CarbonComputers/Cybert/Hardware/Display/YX40006ACT Display Spec/LCD/时序参考timing.png

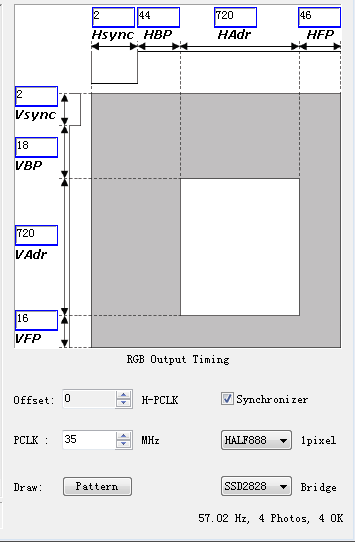
Hardware/Display/YX40006ACT Display Spec/LCD/时序参考timing.png
