CarbonComputers/Cybert/Hardware/PCB/Cybert 3.0 Back.jpg

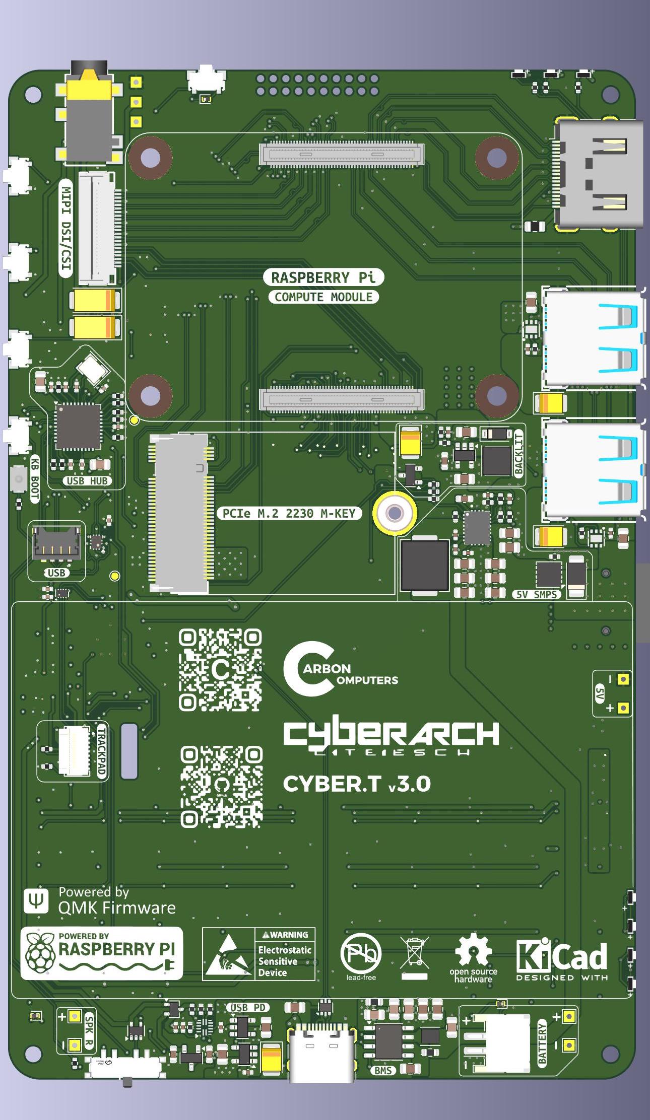
Hardware/PCB/Cybert 3.0 Back.jpg
