CarbonComputers/Cybert/Hardware/PCB/Cybert 3.0 Front.jpg

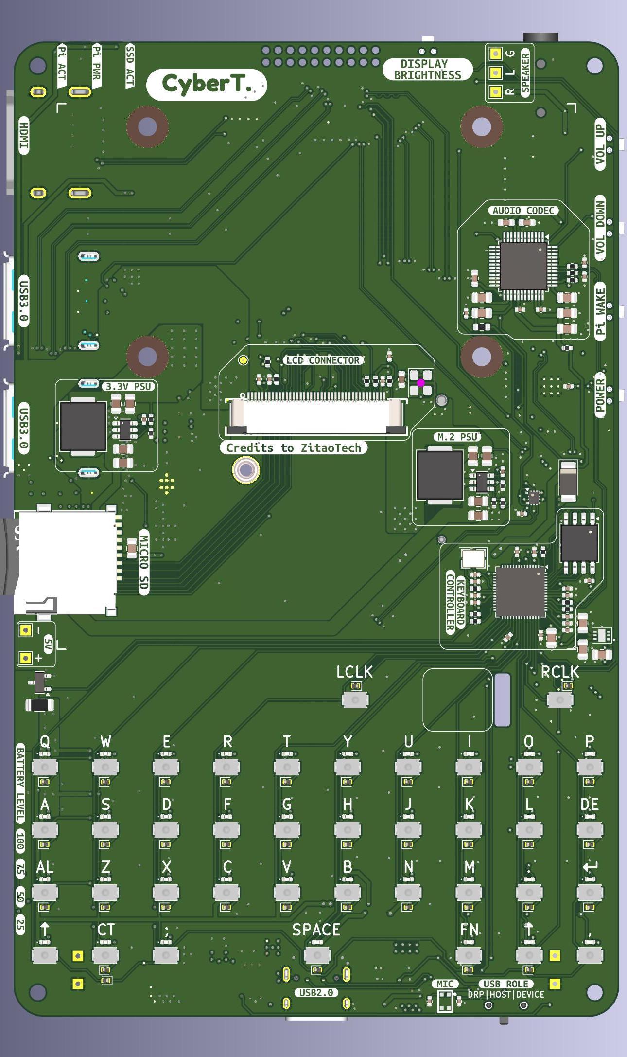
Hardware/PCB/Cybert 3.0 Front.jpg
