CarbonComputers/Cybert/Hardware/Renders/1.jpg

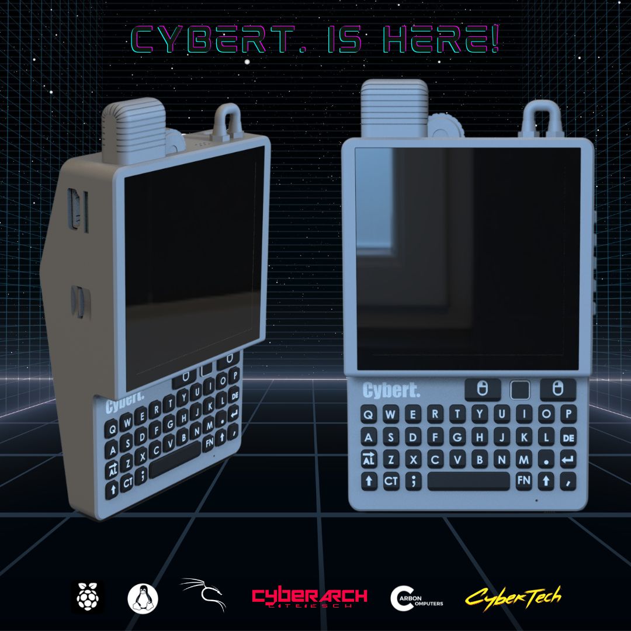
Hardware/Renders/1.jpg
