CarbonComputers/Cybert/Hardware/Renders/2.jpg

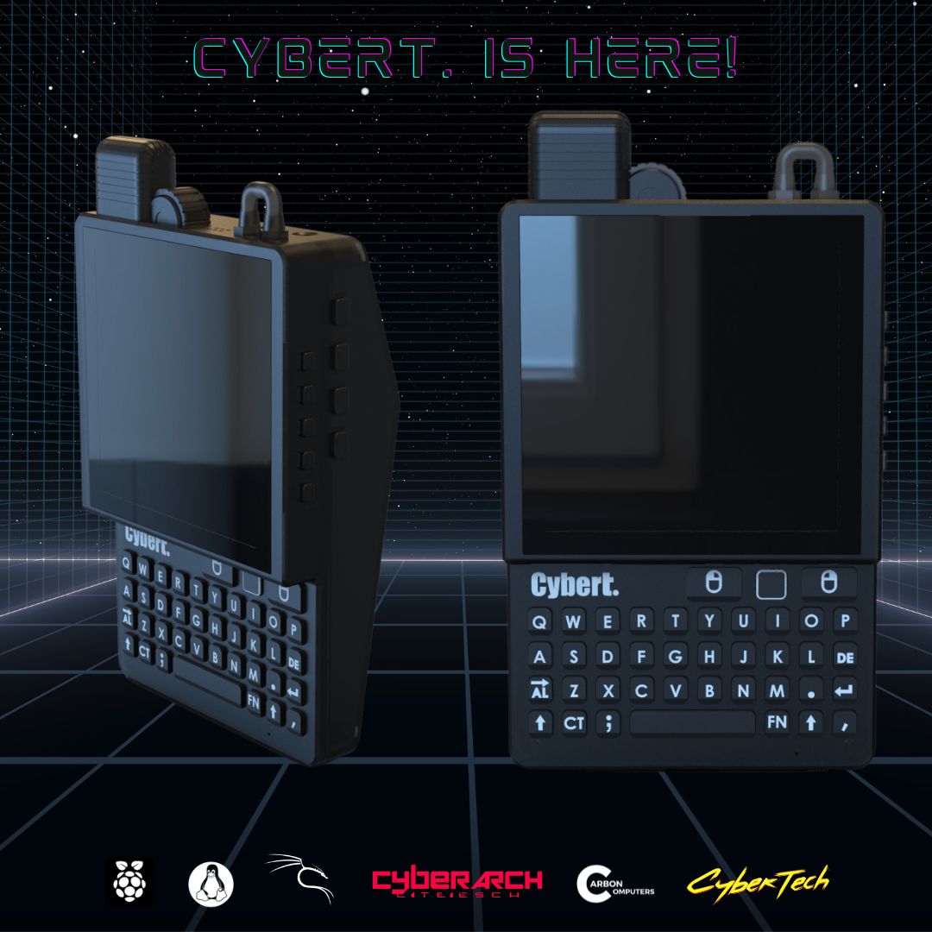
Hardware/Renders/2.jpg
