CarbonComputers/Cybert/Hardware/Renders/5.jpg

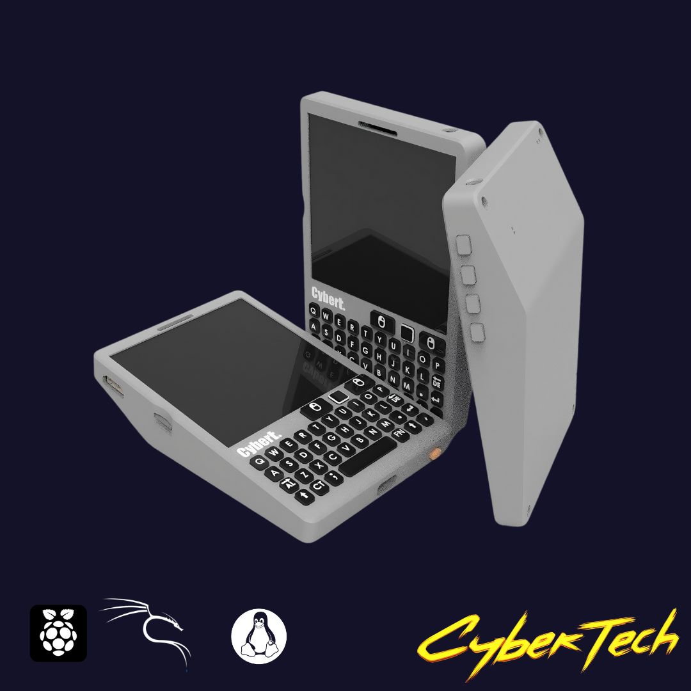
Hardware/Renders/5.jpg
