CarbonComputers/Cybert/Hardware/Renders/6.jpg

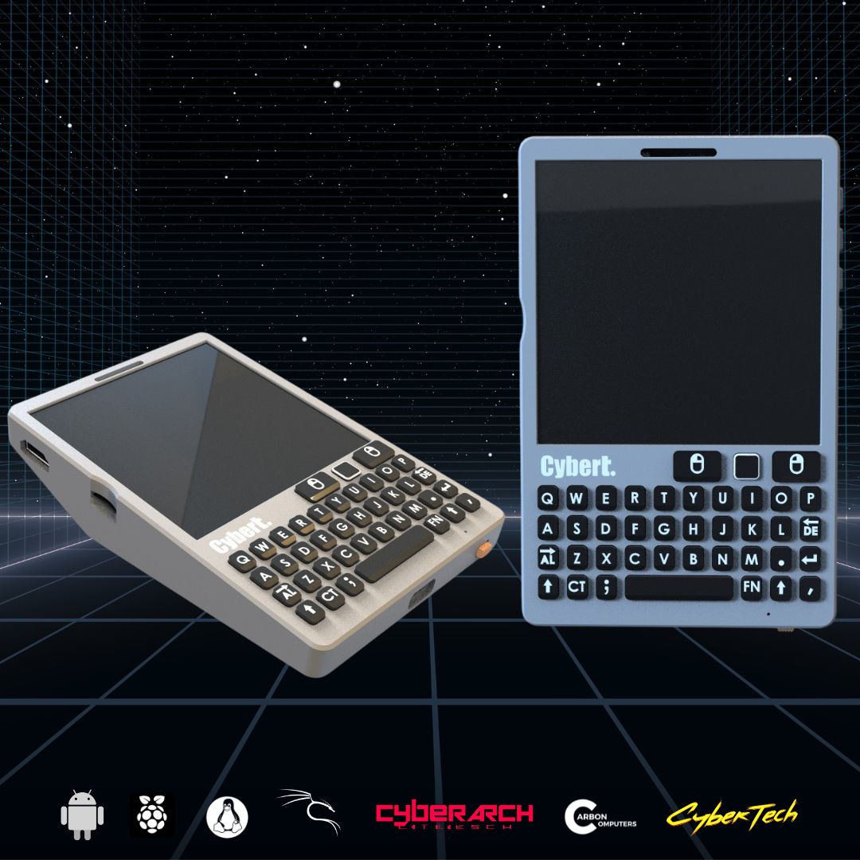
Hardware/Renders/6.jpg
