CarbonComputers/Cybert/Hardware/Renders/7.jpg

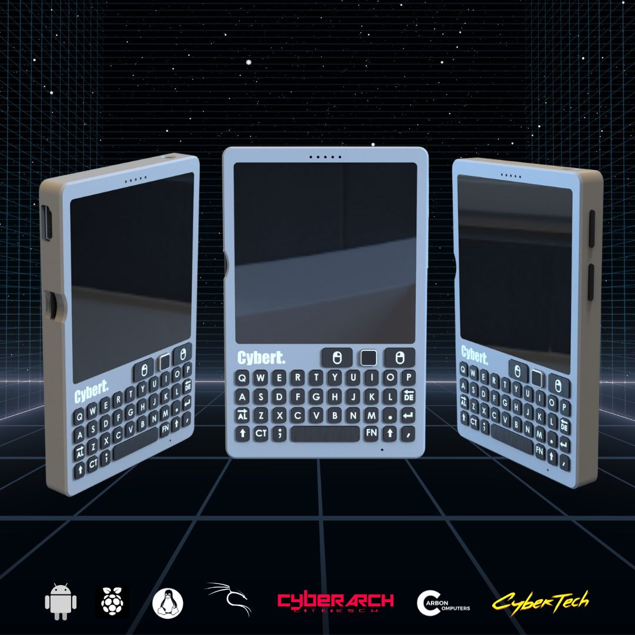
Hardware/Renders/7.jpg
