CarbonComputers/Cybert/Hardware/Renders/18.jpg

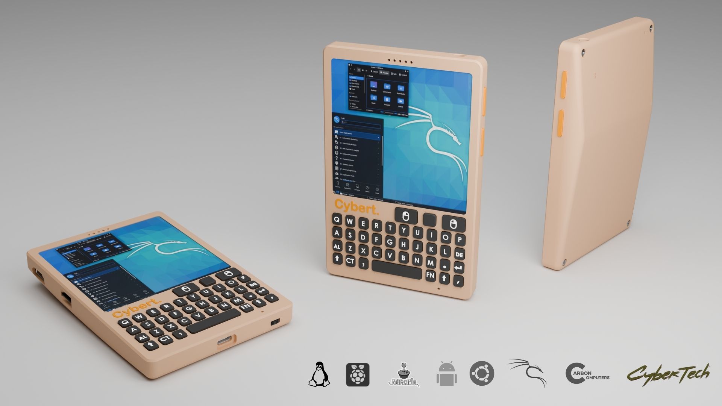
Hardware/Renders/18.jpg
