CarbonComputers/Cybert/Hardware/Renders/19.jpg

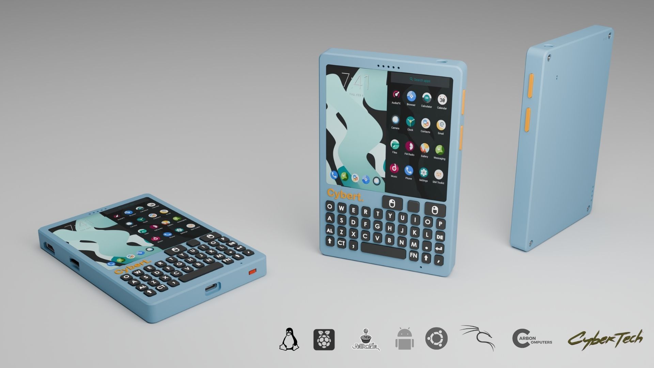
Hardware/Renders/19.jpg
