CarbonComputers/Cybert/Hardware/Renders/20.jpg

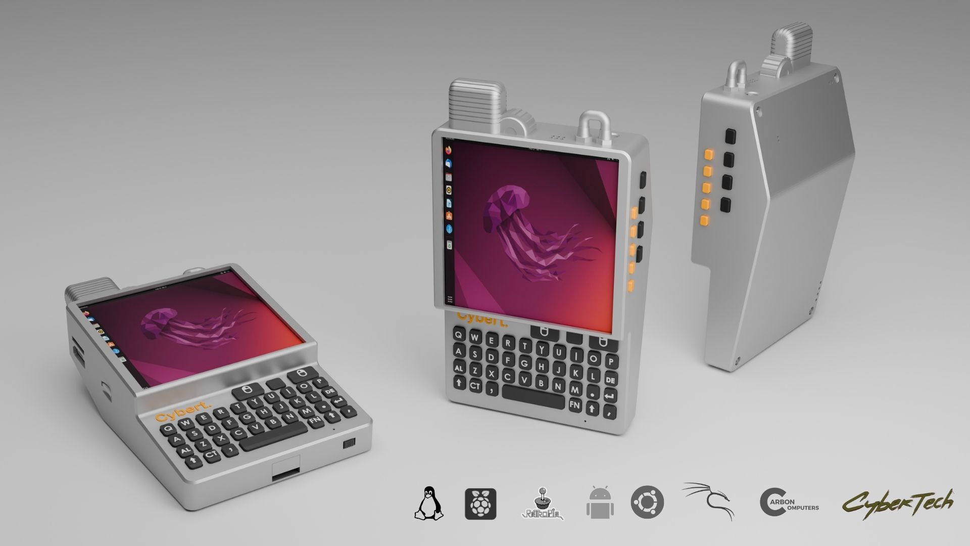
Hardware/Renders/20.jpg
