CarbonComputers/Cybert/Hardware/Renders/21.jpg

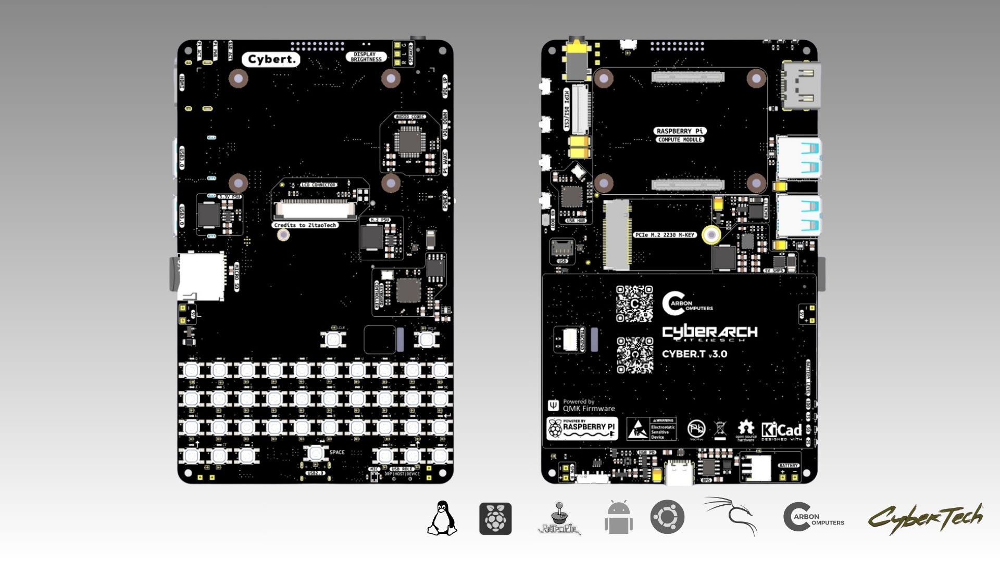
Hardware/Renders/21.jpg
