CarbonComputers/Cybert/Hardware/Renders/Cybert 3.2.1.jpeg

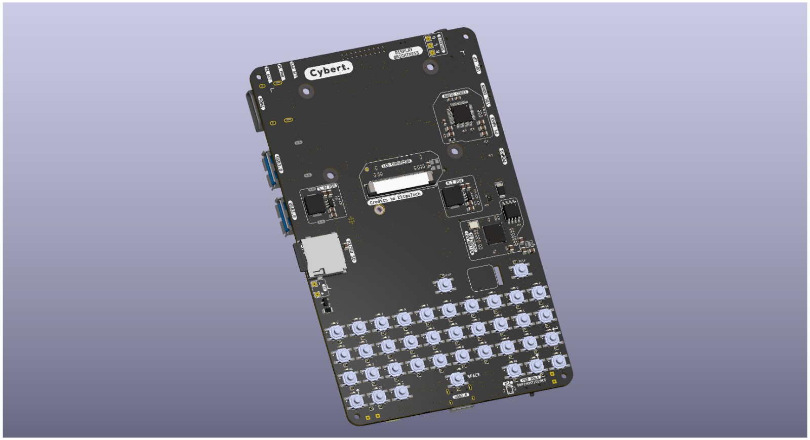
Hardware/Renders/Cybert 3.2.1.jpeg
