CarbonComputers/Cybert/Hardware/Renders/Cybert 3.2.2.jpeg

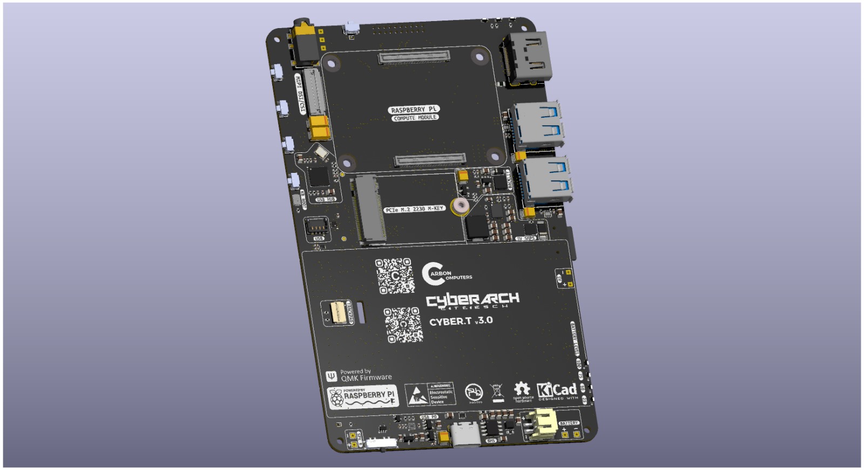
Hardware/Renders/Cybert 3.2.2.jpeg
