CarbonComputers/Cybert/Hardware/Renders/Cybert 3.2.3.jpeg

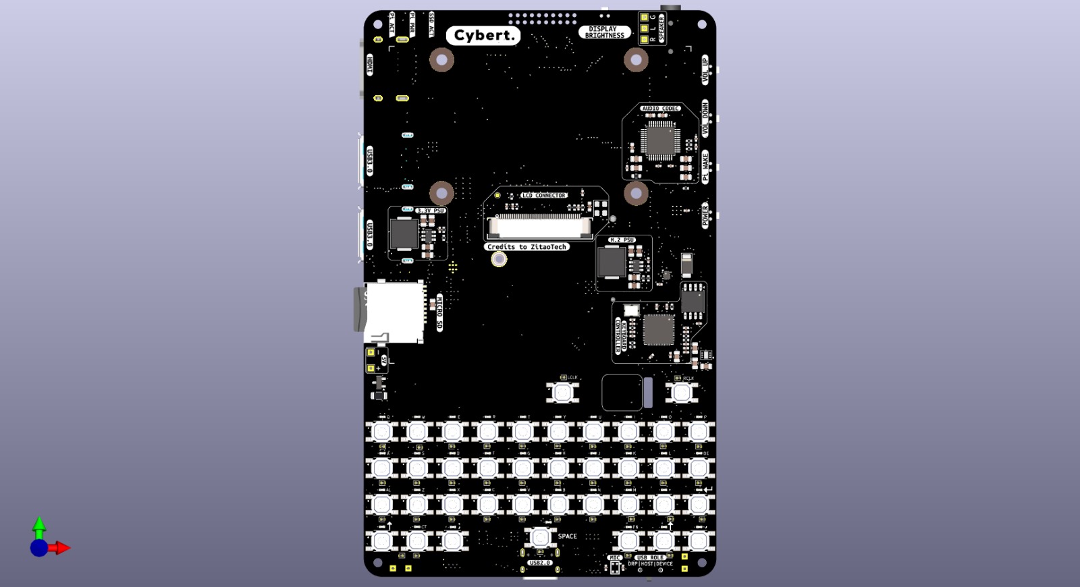
Hardware/Renders/Cybert 3.2.3.jpeg
