CarbonComputers/Cybert/Hardware/Renders/CyberT (5).png

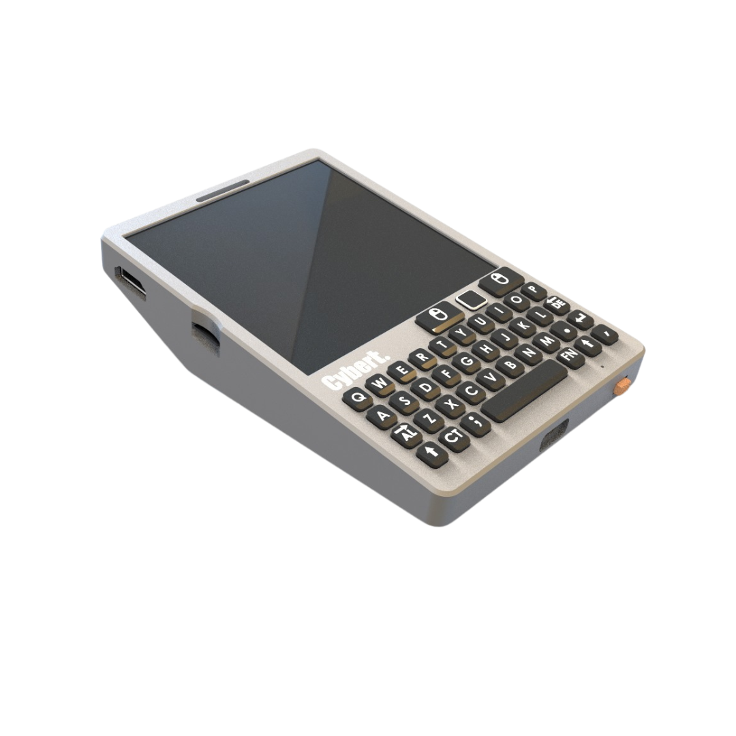
Hardware/Renders/CyberT (5).png
