CarbonComputers/Cybert/Hardware/Renders/Cybert front.png

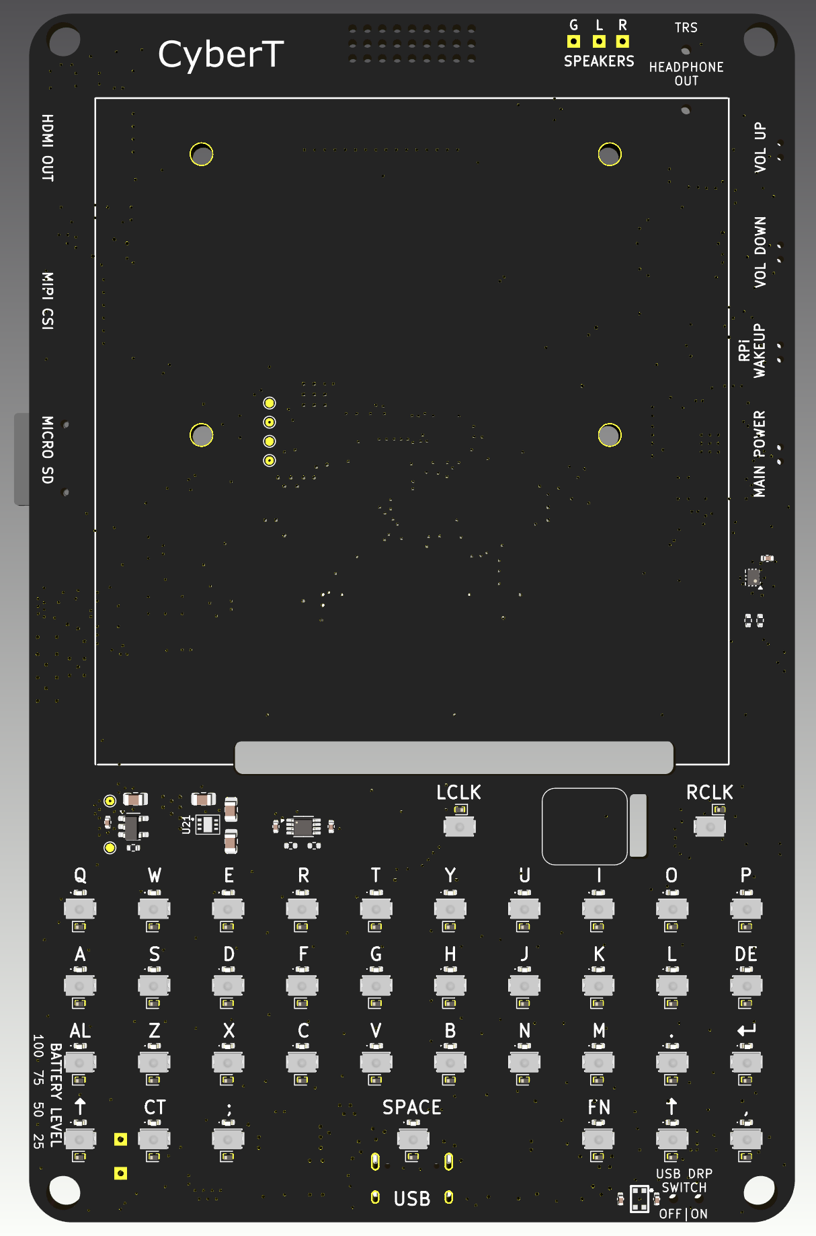
Hardware/Renders/Cybert front.png
