CarbonComputers/Cybert/Hardware/Renders/cyberT_HDMI_v2.273.jpg

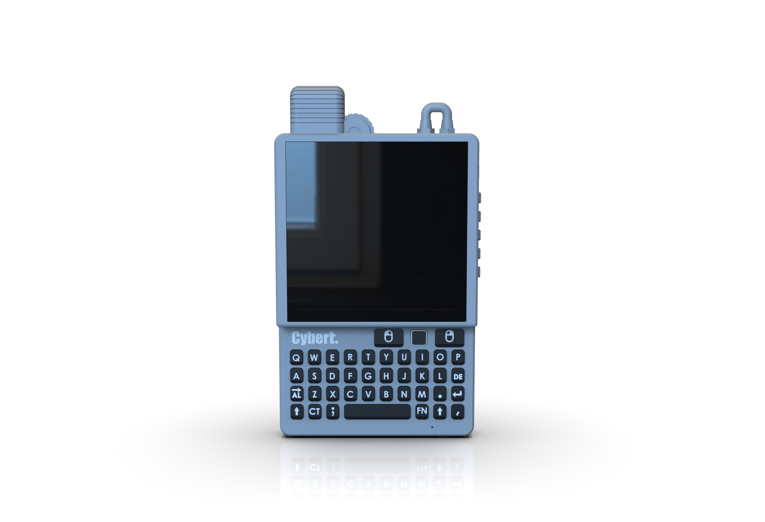
Hardware/Renders/cyberT_HDMI_v2.273.jpg
