CarbonComputers/Cybert/Hardware/Renders/cyberT_slim_v3 - drawing.jpg

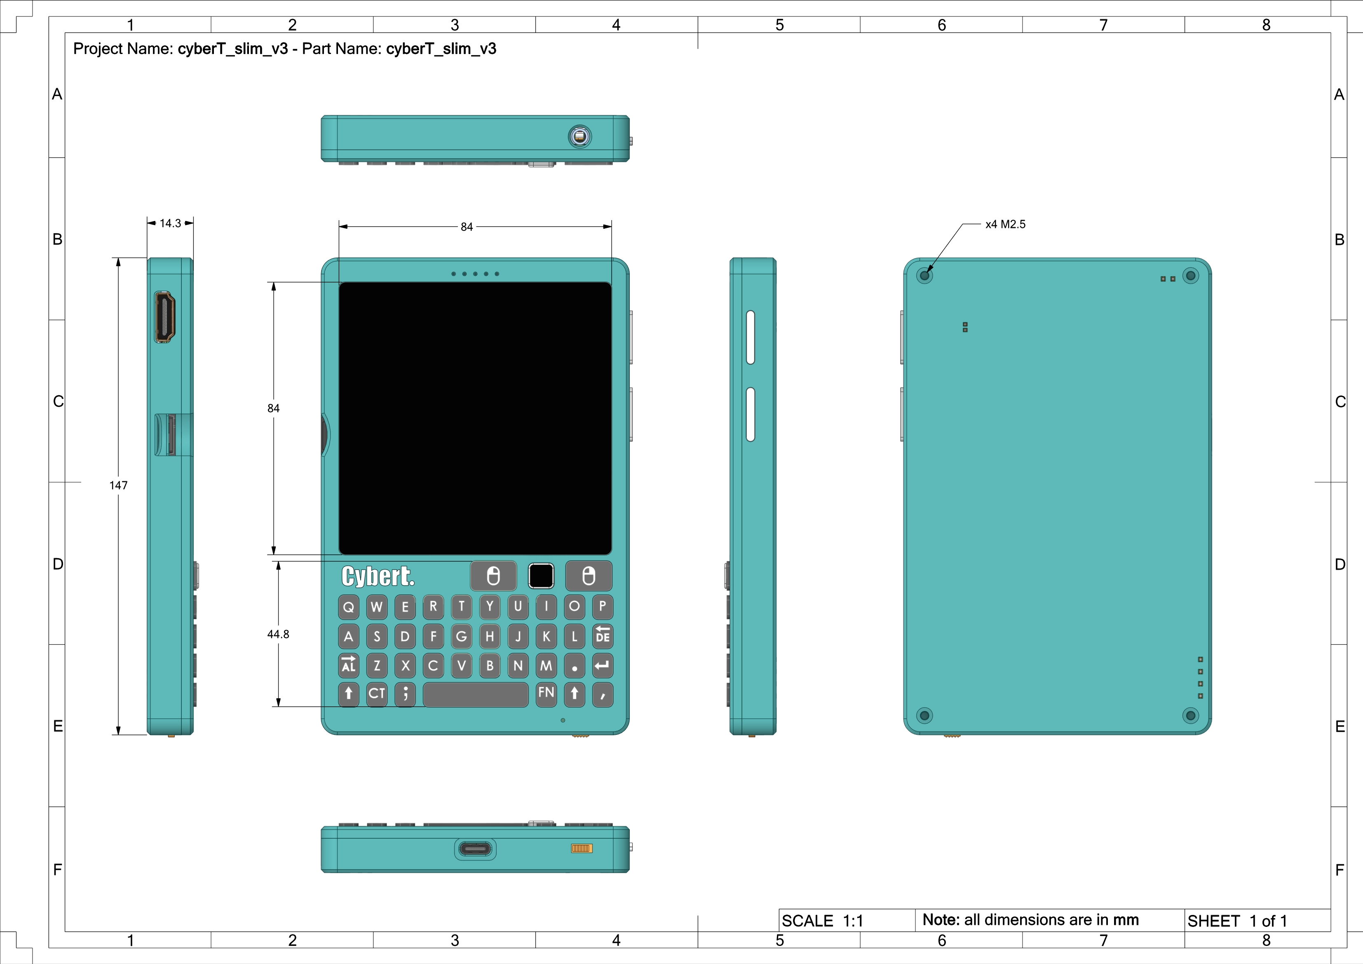
Hardware/Renders/cyberT_slim_v3 - drawing.jpg
