CarbonComputers/Cybert/Hardware/Renders/cyberT_slim_v3.286.jpg

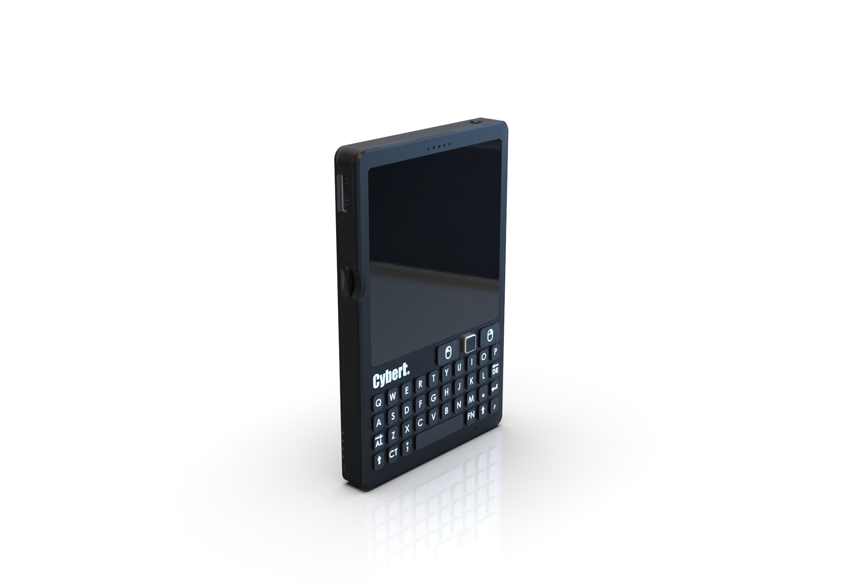
Hardware/Renders/cyberT_slim_v3.286.jpg
