CarbonComputers/Cybert/Hardware/Renders/cyberT_slim_v3.289.jpg

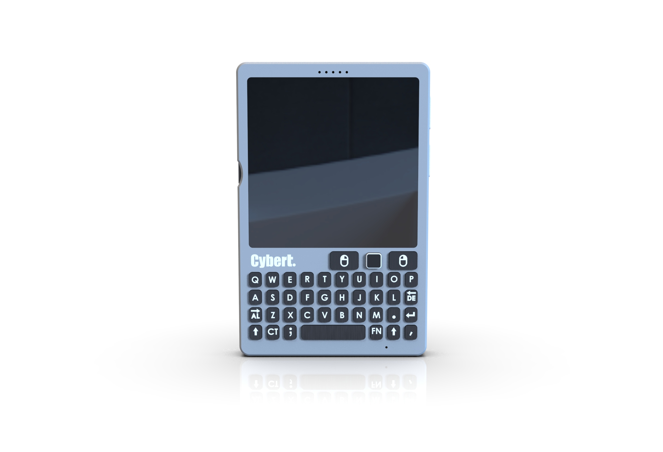
Hardware/Renders/cyberT_slim_v3.289.jpg
