CarbonComputers/Cybert/Hardware/Renders/upscalemedia-transformed.jpeg

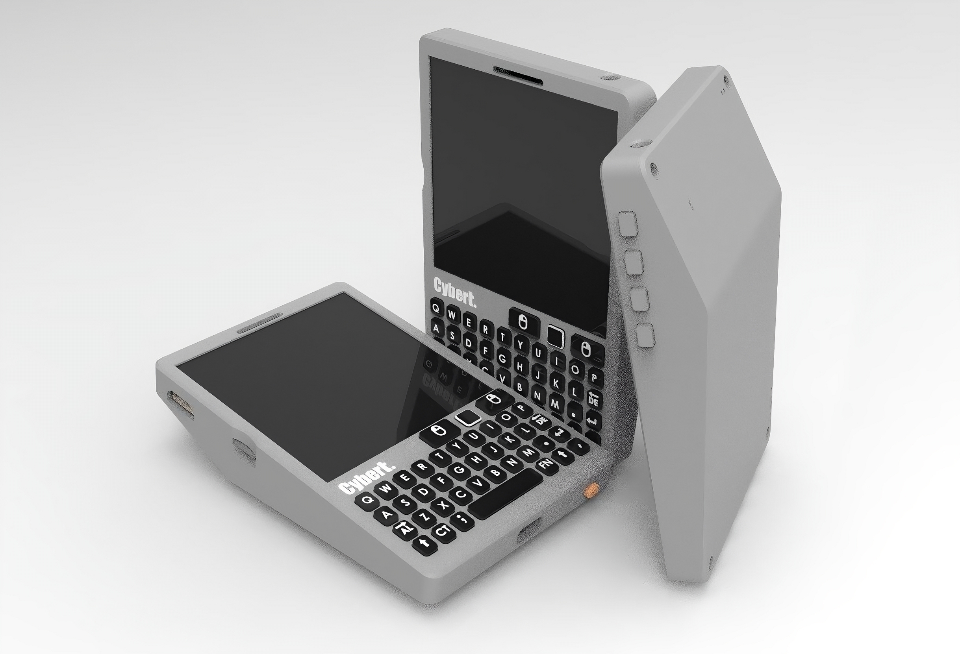
Hardware/Renders/upscalemedia-transformed.jpeg
